OscarPF22/Biped-Robot-Arduino-Project/analog_pid_IMU_esp32_v2/servo_robot.cpp

#include "servo_robot.h"

Servo Servo_Array[NUM_SERVOS];

void RobotInitialize()
{
  //Creado dentro de la función para uso mas eficiente de la meoria
  double Servo_Valores[NUM_SERVOS] = { rodillaR_ini, tobilloR_ini, caderaR_ini, cadera2R_ini, rodillaL_ini, tobilloL_ini, caderaL_ini, cadera2L_ini };
                                          
  for(int i = 0; i < (NUM_SERVOS/2); i++)
  {
     Servo_Array[i].write(Servo_Valores[i]);
     Servo_Array[i+(NUM_SERVOS/2)].write(Servo_Valores[i+(NUM_SERVOS/2)]);
     
     Serial.println("Servos Inicializados...");
     
     delay(200); // delay de 200 ms entre cada movimiento de motor para no demandar excesiva corriente
  }
}
